ole00/tick-led/img/tl007-face_fixing_bolts.jpg

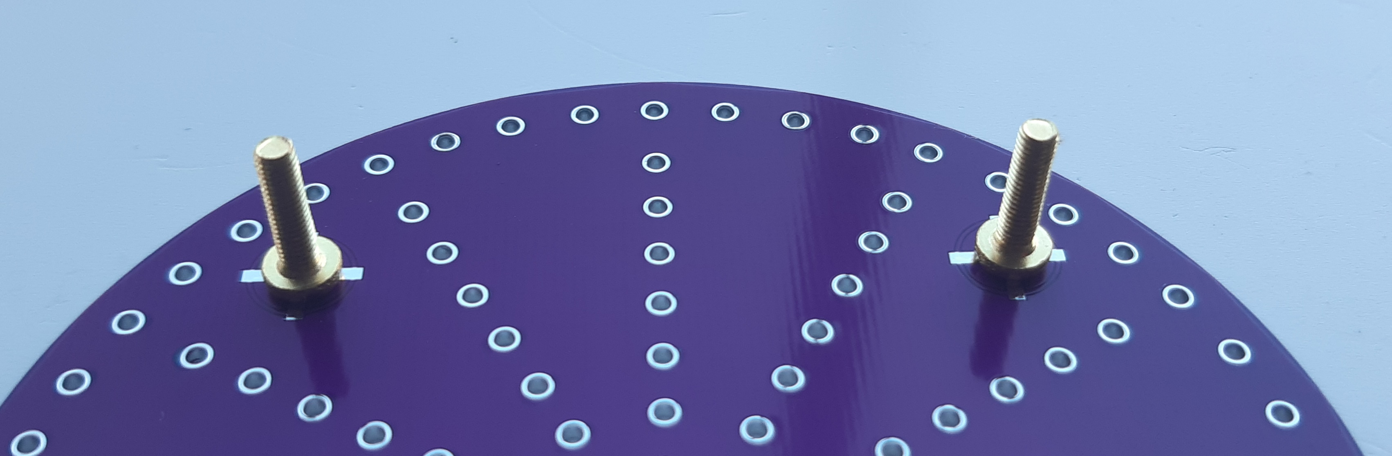
img/tl007-face_fixing_bolts.jpg
