ole00/tick-led/img/tl009-front2.jpg

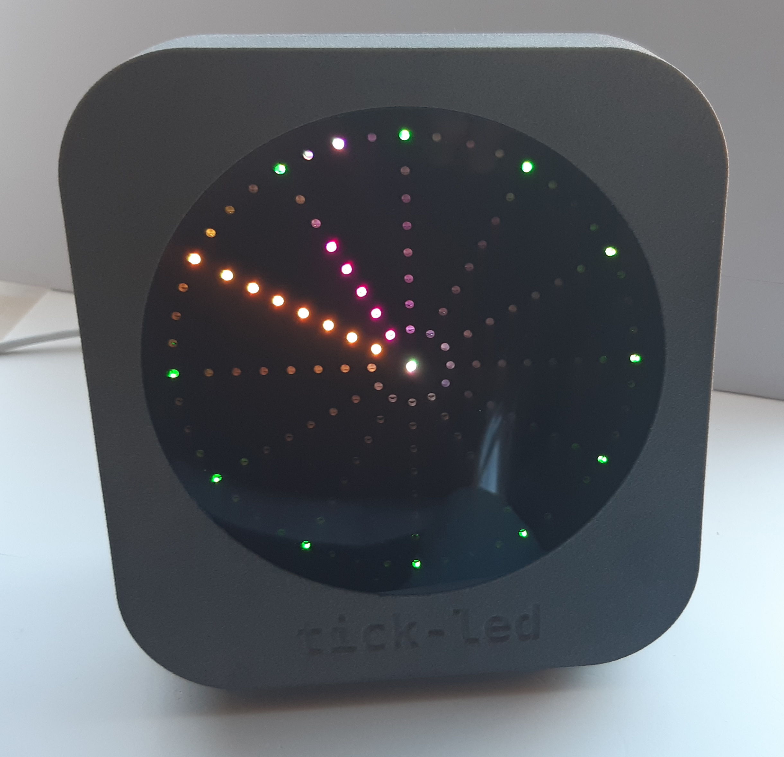
img/tl009-front2.jpg
