ole00/tick-led/img/tl012-oscad_both.jpg

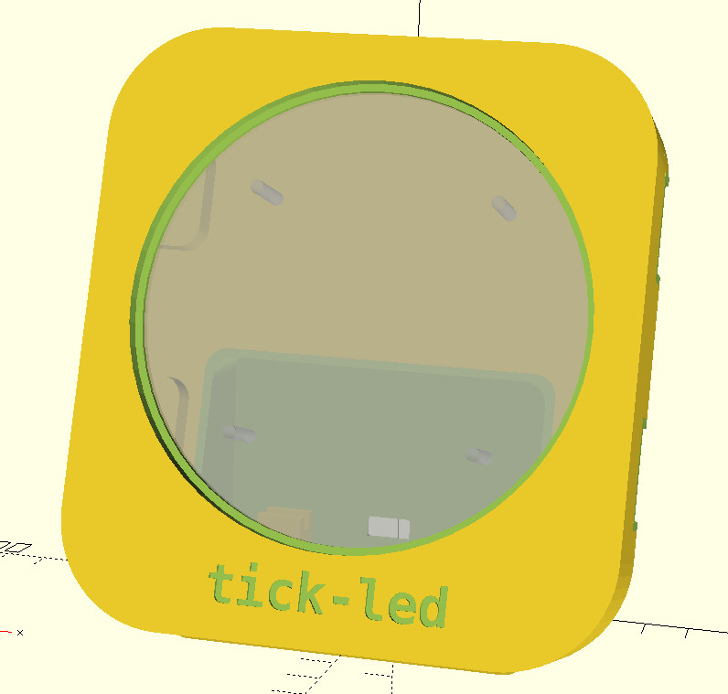
img/tl012-oscad_both.jpg
