ole00/tick-led/img/tl013-oscad_back2.jpg

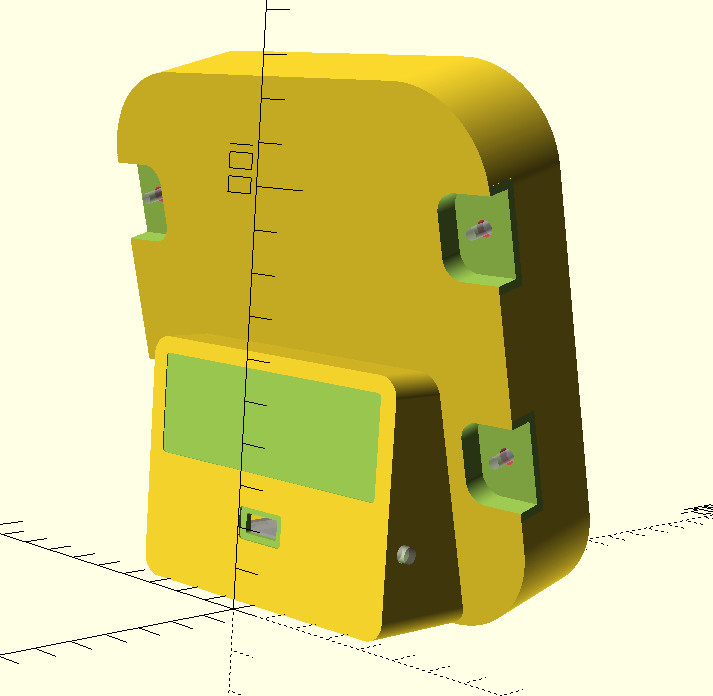
img/tl013-oscad_back2.jpg
