ole00/tick-led/img/tl015-arduino_ide_board.jpg

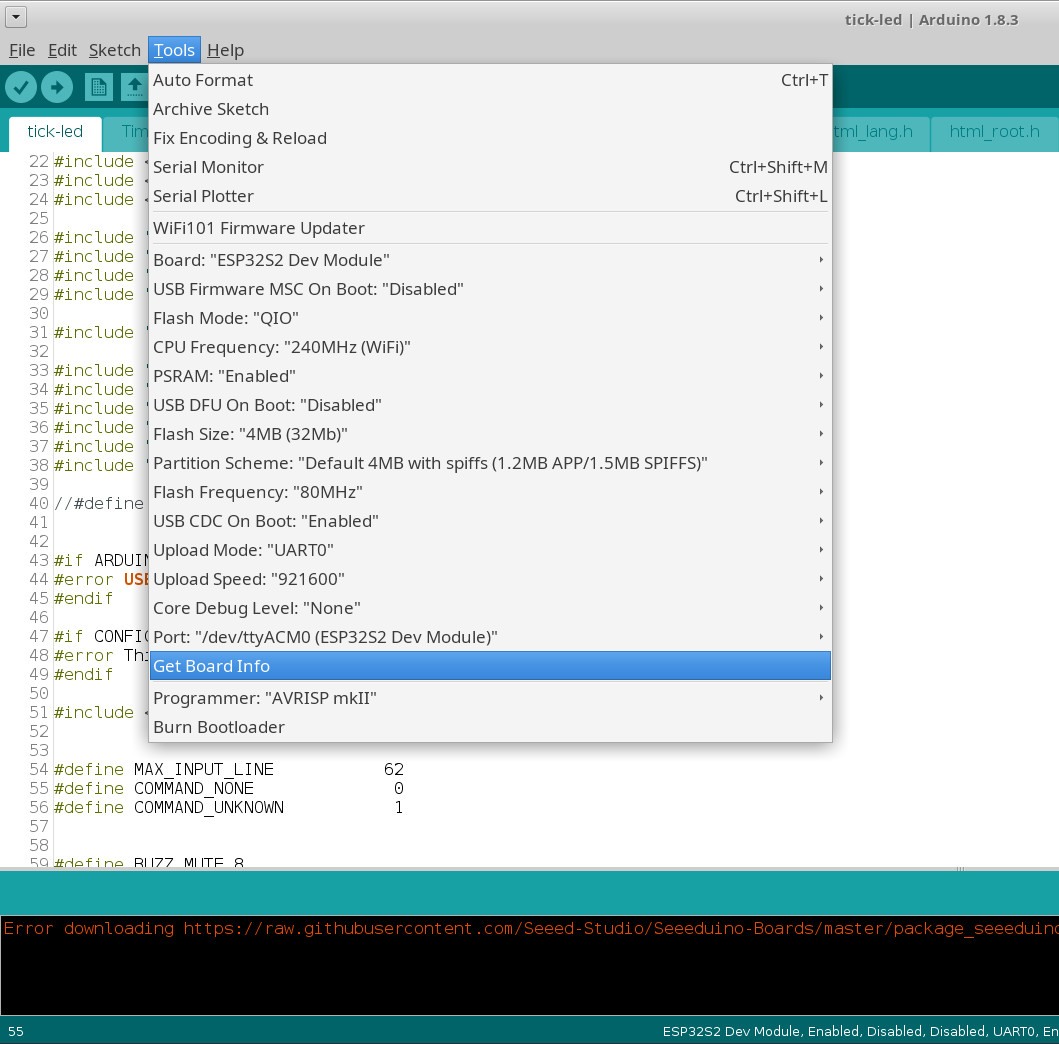
img/tl015-arduino_ide_board.jpg
