ole00/tick-led/img/tl001-led_pcb_soldered.jpg

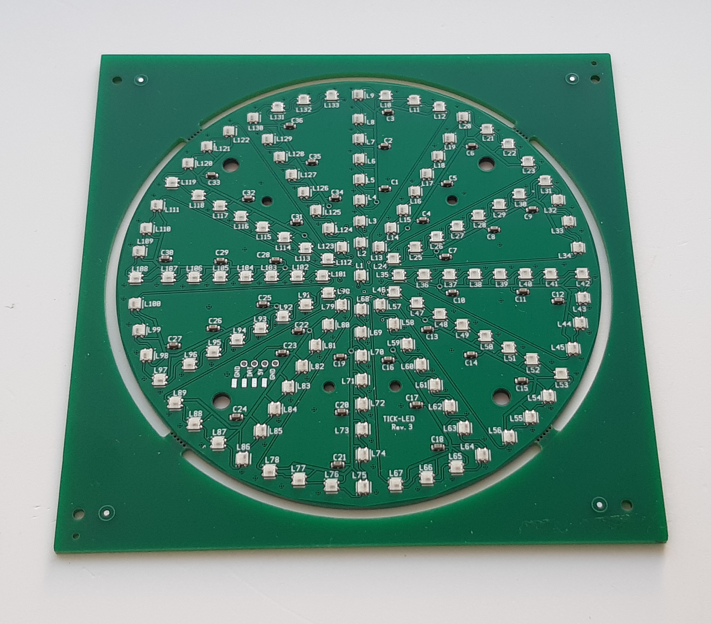
img/tl001-led_pcb_soldered.jpg
