ole00/tick-led/img/tl002-led_pcb_installed.jpg

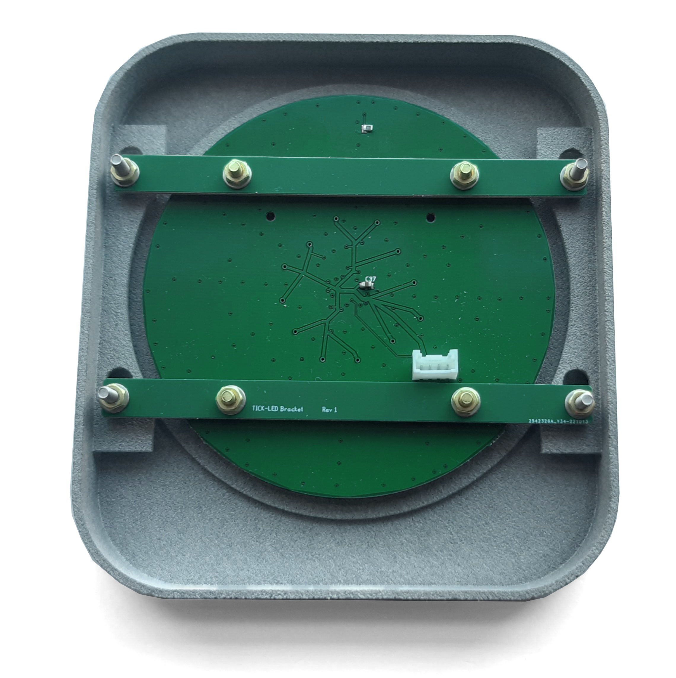
img/tl002-led_pcb_installed.jpg
