ole00/tick-led/img/tl003-mcu_pcb_installed.jpg

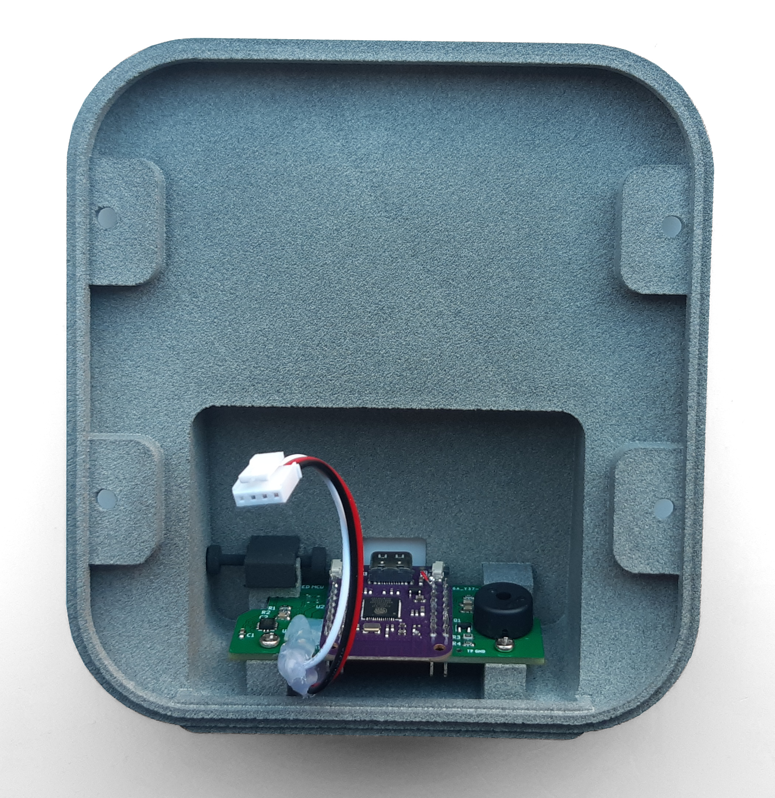
img/tl003-mcu_pcb_installed.jpg
