ole00/tick-led/img/tl004-mcu_pcb_installed_detail.jpg

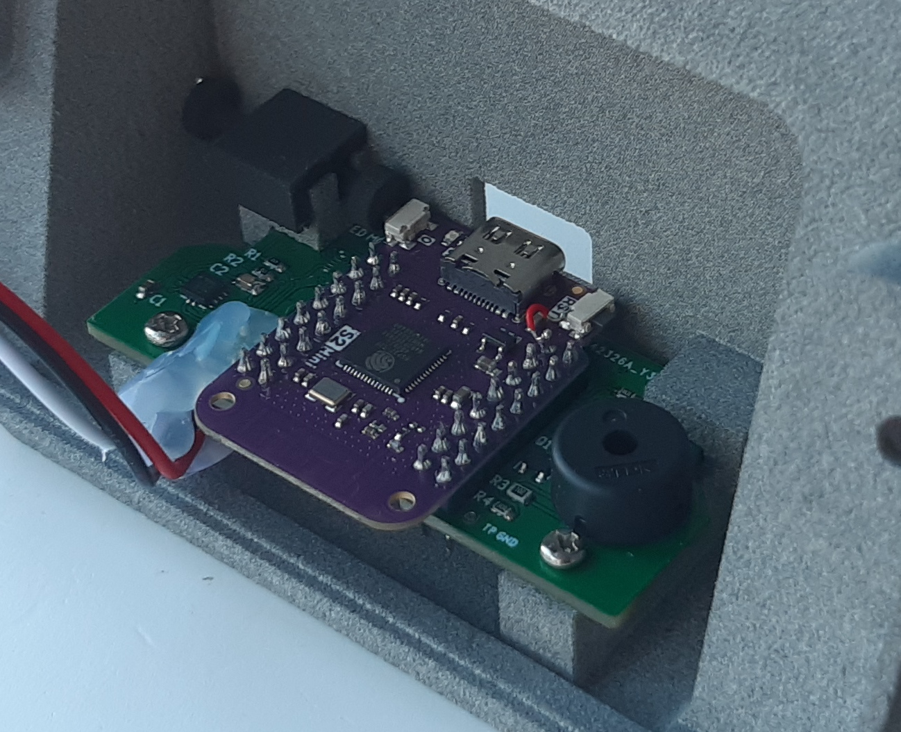
img/tl004-mcu_pcb_installed_detail.jpg
