ole00/tick-led/arduino_fw/html_lang.h

#ifndef _HTML_LANG_H_
#define  _HTML_LANG_H_

static const char* langroot_en[] {
    "Clock configuration:", /* 0 */
    "Language", /* 1 */
    "Apply Language", /* 2 */
    "Server connection (to access this page)", /* 3 */
    "SSID", /* 4 */
    "Password", /* 5 */
    "WiFi Client connection (to get NTP time)", /* 6 */
    "NTP Host", /* 7 */
    "NTP Connection Rate (time sync)", /* 8 */
    "do not sync time", /* 9 */
    "every day", /* 10 */
    "every other day", /* 11 */
    "once a week", /* 12 */
    "Time zone", /* 13 */
    "Time zone offset (in minutes)", /* 14 */
    "Daylight saving offset (in minutes)", /* 15 */
    "Daylight saving rule", /* 16 */
    "No daylight saving", /* 17 */
    "Central Europe: Last Sun March 2:00 / Last Sun October 3:00", /* 18 */
    "Eastern Europe: Last Sun March 3:00 / Last Sun October 4:00", /* 19 */
    "Western Europe: Last Sun March 1:00 / Last Sun October 2:00", /* 20 */
    "Azores: Last Sun March 0:00 / Last Sun October 1:00", /* 21 */
    "Greenland: Last Sat March 22:00 / Last Sat October 23:00", /* 22 */
    "USA: Second Sun March 2:00 / First Sun November 2:00", /* 23 */
    "Cuba: Second Sun March 0:00 / First Sun November 1:00", /* 24 */
    "Mexico: First Sun April 2:00 / Last Sun October 2:00", /* 25 */
    "Australia: First Sun October 2:00 / First Sun April 3:00", /* 26 */
    "New Zealand: Last Sun September 2:00 / First Sun April 3:00", /* 27 */
    "Samoa: Last Sun September 3:00 / First Sun April 4:00", /* 28 */
    "Chile: Second Sun August 0:00 / Second Sun May 0:00", /* 29 */
    "Chile Easter Island: Second Sun August 22:00 / Second Sun May 22:00", /* 30 */
    "Paraguay: First Sun October 0:00 / Last Sun March 0:00", /* 31 */
    "Fiji, Tonga: First Sun November 2:00 / Third Sun January 3:00", /* 32 */
    "Lebanon: Last Sun March 0:00 / Last Sun October 0:00", /* 33 */
    "Jordan: Last Thu February 0:00 / Last Fri October 1:00", /* 34 */
    "Palestine: Last Sat March 1:00 / Last Sat October 1:00", /* 35 */
    "Syria: Last Fri March 0:00 / Last Fri October 0:00", /* 36 */
    "Clock face", /* 37 */
    "Color scheme", /* 38 */
    "default", /* 39 */
    "orange", /* 40 */
    "fandango", /* 41 */
    "red", /* 42 */
    "green", /* 43 */
    "icy", /* 44 */
    "random every day", /* 45 */
    "random every hour", /* 46 */
    "random every 5 min.", /* 47 */
    "random every minute", /* 48 */
    "Minute style", /* 49 */
    "no individual minutes shown", /* 50 */
    "minutes full bar", /* 51 */
    "minutes dot", /* 52 */
    "Seconds style", /* 53 */
    "no seconds shown", /* 54 */
    "single dot", /* 55 */
    "floating", /* 56 */
    "Outer ring style", /* 57 */
    "hidden", /* 58 */
    "4 dots", /* 59 */
    "12 dots", /* 60 */
    "Visual settings", /* 61 */
    "Brightness", /* 62 */
    "Display dimming", /* 63 */
    "no dimming", /* 64 */
    "medium", /* 65 */
    "low", /* 66 */
    "dark except the central dot", /* 67 */
    "dark completely", /* 68 */
    "Dim from time", /* 69 */
    "Dim until time", /* 70 */
    "Hand animation", /* 71 */
    "no animation", /* 72 */
    "fade out/fade in", /* 73 */
    "retract/grow", /* 74 */
    "bubble", /* 75 */
    "Alarm settings", /* 76 */
    "Alarm sound pitch", /* 77 */
    "high", /* 78 */
    "Alarm 1", /* 79 */
    "Disabled", /* 80 */
    "Mon", /* 81 */
    "Tue", /* 82 */
    "Wed", /* 83 */
    "Thu", /* 84 */
    "Fri", /* 85 */
    "Sat", /* 86 */
    "Sun", /* 87 */
    "Mon - Fri", /* 88 */
    "Sat - Sun", /* 89 */
    "Every day", /* 90 */
    "1 slow beep", /* 91 */
    "2 beeps", /* 92 */
    "4 quick beeps", /* 93 */
    "until stopped", /* 94 */
    "ring 1x", /* 95 */
    "ring 2x", /* 96 */
    "ring 3x", /* 97 */
    "ring 5x", /* 98 */
    "ring 10x", /* 99 */
    "ring 20x", /* 100 */
    "ring 30x", /* 101 */
    "ring 40x", /* 102 */
    "ring 50x", /* 103 */
    "ring 100x", /* 104 */
    "ring 300x", /* 105 */
    "Alarm 2", /* 106 */
    "Alarm 3", /* 107 */
    "Alarm 4", /* 108 */
    "Alarm 5", /* 109 */
    "Button config", /* 110 */
    "Short press (less than 0.5 sec.)", /* 111 */
    "brightness change", /* 112 */
    "color scheme change", /* 113 */
    "hand animation change", /* 114 */
    "Medium press (1 - 2 sec.)", /* 115 */
    "Save Configuration", /* 116 */
    "" // terminator
};


static const char* langroot_cz[] {
    "Nastaveni hodin:",
    "Jazyk",
    "Zmen jazyk",
    "Pripojeni k serveru (pristup na tuto stranku)",
    "SSID",
    "Heslo",
    "WiFi Internetove pripojeni (zjisteni casu)",
    "NTP Server",
    "NTP Pripojeni (jak casto)",
    "nepripojovat k serveru",
    "kazdy den",
    "kazdy druhy den",
    "jednou tydne",
    "Casova zona",
    "Rozdil casove zony (v minutach)",
    "Rozdil letniho casu (v minutach)",
    "Pravidlo zmeny letniho a zimniho casu",
    "Nepouzivat letni a zimni cas",
    "Centralni Evropa: Posledni Ned Brezen 2:00 / Posledni Ned Rijen 3:00",
    "Vychodni Evropa: Posledni Ned Brezen 3:00 / Posledni Ned Rijen 4:00",
    "Zapadni Evropa: Posledni Ned Brezen 1:00 / Posledni Ned Rijen 2:00",
    "Azory: Posledni Ned Brezen 0:00 / Posledni Ned Rijen 1:00",
    "Gronsko: Posledni Sob Brezen 22:00 / Posledni Sob Rijen 23:00",
    "USA: Druha Ned Brezen 2:00 / Prvni Ned Listopad 2:00",
    "Kuba: Druha Ned Brezen 0:00 / Prvni Ned Listopad 1:00",
    "Mexiko: Prvni Ned Duben 2:00 / Posledni Ned Rijen 2:00",
    "Australie: Prvni Nedele Rijen 2:00 / Prvni Ned Duben 3:00",
    "Novy Zeland: Posledni Ned Zari 2:00 / Prvni Ned Duben 3:00",
    "Samoa: Posledni Ned Zari 3:00 / Prvni Ned Duben 4:00",
    "Chile: Druha Ned Srpen 0:00 / Druha Ned Kveten 0:00",
    "Chile Velikon. Ostrov: Druha Ned Srpen 22:00 / Druha Ned Kveten 22:00",
    "Paraguay: Prvni Ned Rijen 0:00 / Posledni Ned Brezen 0:00",
    "Fiji, Tonga: Prvni Ned Listopad 2:00 / Treti Ned Leden 3:00",
    "Libanon: Posledni Ned Brezen 0:00 / Posledni Ned Rijen 0:00",
    "Jordansko: Posletni Ctv Unor 0:00 / Posledni Pat Rijen 1:00",
    "Palestina: Posledni Sob Brezen 1:00 / Posladni Sob Rijen 1:00",
    "Syrie: Posledni Pat Brezen 0:00 / Posledni Pat Rijen 0:00",
    "Cifernik hodin",
    "Barevne schema",
    "zakladni",
    "oranzove",
    "svestka",
    "cervene",
    "zelene",
    "ledove",
    "nahodne kazdy den",
    "nahodne kazdou hodinu",
    "nahodne kazdych 5 min.",
    "nahodne kazdou minutu",
    "Styl minutovky",
    "minuty se nezobrazuji",
    "minuty: plna cara",
    "minuty: jedna tecka",
    "Styl vterinovky",
    "vteriny se nezobrazuji",
    "jedna tecka",
    "plovouci",
    "Styl vnejsiho kruhu",
    "skryty",
    "4 tecky",
    "12 tecek",
    "Vizualni nastaveni",
    "Jas displeje",
    "Setmeni displeje",
    "nestmivat",
    "stredni",
    "nizky",
    "pouze stredni tecka",
    "uplne setmely",
    "Setmet od casu",
    "Setmet do casu",
    "Animace rucicky",
    "bez animace",
    "plynuly prechod",
    "zkratit/narust",
    "probublat",
    "Nastaveni Budiku",
    "Vyska tonu budiku",
    "vysoky",
    "Alarm 1",
    "vypnuty",
    "Po",
    "Ut",
    "St",
    "Ct",
    "Pa",
    "So",
    "Ne",
    "Po - Pa",
    "So - Ne",
    "Kazdy den",
    "1 pomale pipnuti",
    "2 pipnuti",
    "4 rychla pipnuti",
    "az do zastaveni",
    "zvon 1x",
    "zvon 2x",
    "zvon 3x",
    "zvon 5x",
    "zvon 10x",
    "zvon 20x",
    "zvon 30x",
    "zvon 40x",
    "zvon 50x",
    "zvon 100x",
    "zvon 300x",
    "Alarm 2",
    "Alarm 3",
    "Alarm 4",
    "Alarm 5",
    "Nastaveni tlacitka",
    "Kratky stisk (mene nez 0,5 sek.)",
    "zmeni jas displeje",
    "zmeni barevne schema",
    "zmeni animaci rucicky",
    "Stredi stisk (1 - 2 sek.)",
    "Ulozit nastaveni",
    "" //terminator
};

static const char* langmisc_en[] {
    "Clock configuration saved OK", /* 0 */
    "The new settings may be applied after the clock restart.", /* 1 */
    "Clock configuration save failed!", /* 2 */
    "Please enter the clock configuration and try again.", /* 3 */
    ""
};

static const char* langmisc_cz[] {
    "Nastaveni hodin bylo ulozeno.", /* 0 */
    "Nektera nastaveni se mohou projevit az po restartu hodin.", /* 1 */
    "Ulozeni nastaveni selhalo!", /* 2 */
    "Spuste nastaveni hodin a zkuste to znovu.", /* 3 */
    ""
};


#endif /* _HTML_LANG_H_ */
