ole00/tick-led/arduino_fw/rttl_tunes.h

// more tunes here:
// http://mines.lumpylumpy.com/Electronics/Computers/Software/Cpp/MFC/RingTones.RTTTL

#ifndef _RTTL_TUNES_H_
#define _RTTL_TUNES_H_

const char rttl_tune_ateam[] = "A-Team:d=8,o=5,b=125:4d#6,a#,2d#6,16p,g#,4a#,4d#.,p,16g,16a#,d#6,a#,f6,2d#6,16p,c#.6,16c6,16a#,g#.,2a#";
const char rttl_tune_richw[] = "Rich Man's World:d=8,o=6,b=112:16e,16p,16e,16p,16e,16p,16e,16p,16e,16p,16e,16p,16e5,16a5,16c,16e,16d#,16p,16d#,16p,16d#,16p,16d#,16p,16d#,16p,16d#,16p,16f5,16a5,16c,16d#,4d,c,a5,c,4c,2a5,32a5,32c,32e,a6,1p";
const char rttl_tune_indyj[] = "Indiana:d=4,o=5,b=250:e,8p,8f,8g,8p.,1c6,8p.,d,8p,8e,1f,p.,g,8p,8a,8b,8p.,1f6,p,a,8p,8b,2c6,2d6,2e6,e,8p,8f,8g,8p.,1c6,p,d6,8p,8e6,1f.6,g,8p,8g,e.6,8p,d6,8p,8g,e.6,8p,d6,8p,8g,f.6,8p,e6,8p,8d6,1c6,1p,2p";
const char rttl_tune_swars[] = "Star Wars:d=4,o=5,b=45:32p,32f#,32f#,32f#,8b.,16f#.6,32e6,32d#6,32c#6,8b.6,16f#.6,32e6,32d#6,32c#6,8b.6,16f#.6,32e6,32d#6,32e6,8c#.6,8p,32f#,32f#,32f#,8b.,16f#.6,32e6,32d#6,32c#6,8b.6,16f#.6,32e6,32d#6,32c#6,8b.6,16f#.6,32e6,32d#6,32e6,8c#.6,8p";
const char rttl_tune_adams[] = "Adams Family:d=8,o=5,b=160:c,4f,a,4f,c,4b4,2g,f,4e,g,4e,g4,4c,2f,c,4f,a,4f,c,4b4,2g,f,4e,c,4d,e,1f,c,d,e,f,1p,d,e,f#,g,1p,d,e,f#,g,4p,d,e,f#,g,4p,c,d,e,f,1p";
const char rttl_tune_bod[]   = "Bod:d=8,o=5,b=200:a,b,a,4c#6,a,4c#6,c#6,4b,16a,16b,16a,e,4p,e,f#,e,4g,4g,4g,4f#,e,2p,a,b,a,4c#6,a,4c#6,c#6,4b,16a,16b,16a,e,4p,e,f#,e,4g,4g,4g,4g,g#,a,b,4e,4p,a,c#6,a,p,f#,e,4p,a,c#6,a,p,f#,e,2p,4f#,4a,4a,4b,4c6,b,a,p,a,b,a,4c#6,a,4c#6,c#6,4b,16a,16b,16a,e,4p,e,f#,e,4g,4g,4g,4g#,a,1p";
const char rttl_tune_dbanj[] = "Duelling Banjos:d=8,o=5,b=200:c#,d,4e,4c#,4d,4b4,4c#,4a4,4b4,4p,16c#6,16p,16d6,16p,e6,p,c#6,p,d6,p,b,p,c#6,p,a,p,4b,4p,4a4,4a4,4b4,4c#,4a4,4c#,4b4,4p,a,p,a,p,b,p,c#6,p,a,p,c#6,p,b,4p";
const char rttl_tune_enter[] = "Entertainer:d=8,o=5,b=140:d,d#,e,4c6,e,4c6,e,2c.6,c6,d6,d#6,e6,c6,d6,4e6,b,4d6,2c6,4p,d,d#,e,4c6,e,4c6,e,2c.6,p,a,g,f#,a,c6,4e6,d6,c6,a,2d6,4p";
const char rttl_tune_gbust[] = "Ghost Busters:d=8,o=5,b=120:16c6,32p,16c6,e6,c6,d6,a#,2p,32c6,32p,32c6,32p,c6,a#,c6,2p";
const char rttl_tune_jbels[] = "Jingle Bells:d=4,o=5,b=170:b,b,b,p,b,b,b,p,b,d6,g.,8a,2b.,8p,c6,c6,c6.,8c6,c6,b,b,8b,8b,b,a,a,b,2a,2d6,p";
const char rttl_tune_kridr[] = "Knight Rider:d=32,o=5,b=63:16e,f,e,8b,16e6,f6,e6,8b,16e,f,e,16b,16e6,4d6,8p,4p,16e,f,e,8b,16e6,f6,e6,8b,16e,f,e,16b,16e6,4f6,4p";
const char rttl_tune_12day[] = "On the 12th Day of christmas:d=8,o=5,b=150:d,d,4g,g,g,4g,g,g,a,b,c6,a,4b.,p,4d6,a,b,c6,a,d6,d6,a,b,c6,a,4d6,4e6,4d.6,p,d6,c6,b,a,4g,a,b,4c6,4e,4e,4d,g,a,b,c6,4b,4a,2g.,p";
const char rttl_tune_popcr[] = "Popcorn:d=16,o=5,b=140:a,p,g,p,a,p,e,p,c,p,e,p,8a4,8p,a,p,g,p,a,p,e,p,c,p,e,p,8a4,8p,a,p,b,p,c6,p,b,p,c6,p,a,p,b,p,a,p,b,p,g,p,a,p,g,p,a,p,f,8a,8p,a,p,g,p,a,p,e,p,c,p,e,p,8a4,8p,a,p,g,p,a,p,e,p,c,p,e,p,8a4,8p,a,p,b,p,c6,p,b,p,c6,p,a,p,b,p,a,p,b,p,g,p,a,p,g,p,a,p,b,4c6,p";
const char rttl_tune_ymca[]  = "YMCA:d=8,o=5,b=160:c#6,a#,2p,a#,g#,f#,g#,a#,4c#6,a#,4c#6,d#6,a#,2p,a#,g#,f#,g#,a#,4c#6,a#,4c#6,d#6,b,2p,b,a#,g#,a#,b,4d#6,f#6,4d#6,4f.6,4d#.6,4c#.6,4b.,4a#,4g#,2p";

#endif /* _RTTL_TUNES_H_ */
